biancapopescu0411/ebook-reader/Images/baterie.png

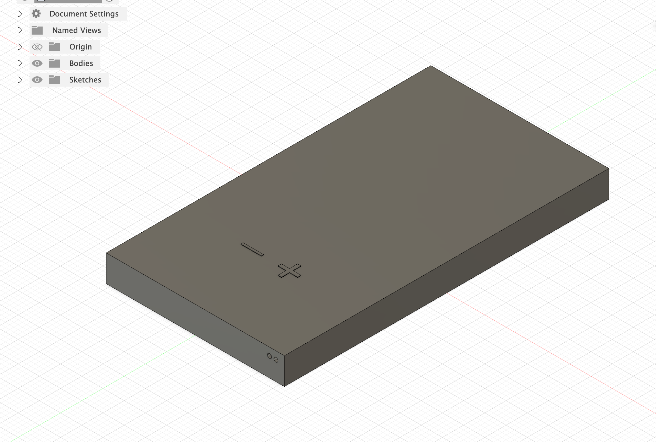
Images/baterie.png
